nithinmathewjoji/Schrodinger-Clock-PCB-Watch-/Images/pcb watch back view 2.png

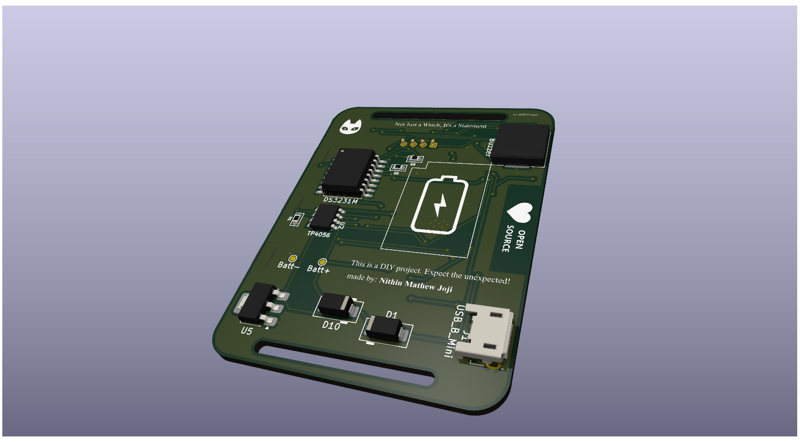
Images/pcb watch back view 2.png
