nithinmathewjoji/Schrodinger-Clock-PCB-Watch-/Images/pcb watch front view.png

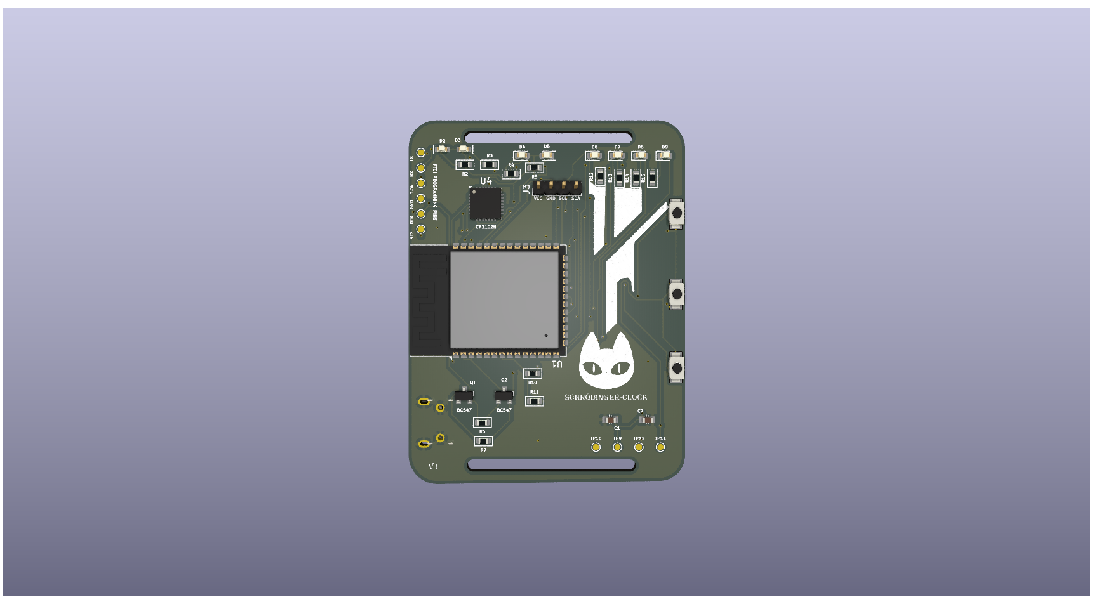
Images/pcb watch front view.png
